charlee/8051-parking-radar/gallery/06-assembled.jpg

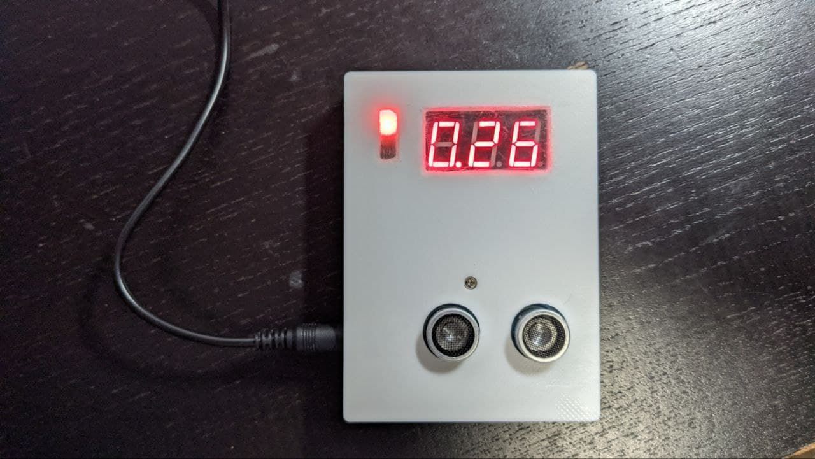
gallery/06-assembled.jpg
